Jin-314/IoT-IdeaKit/board/main/pic/v.1/3D_1.png

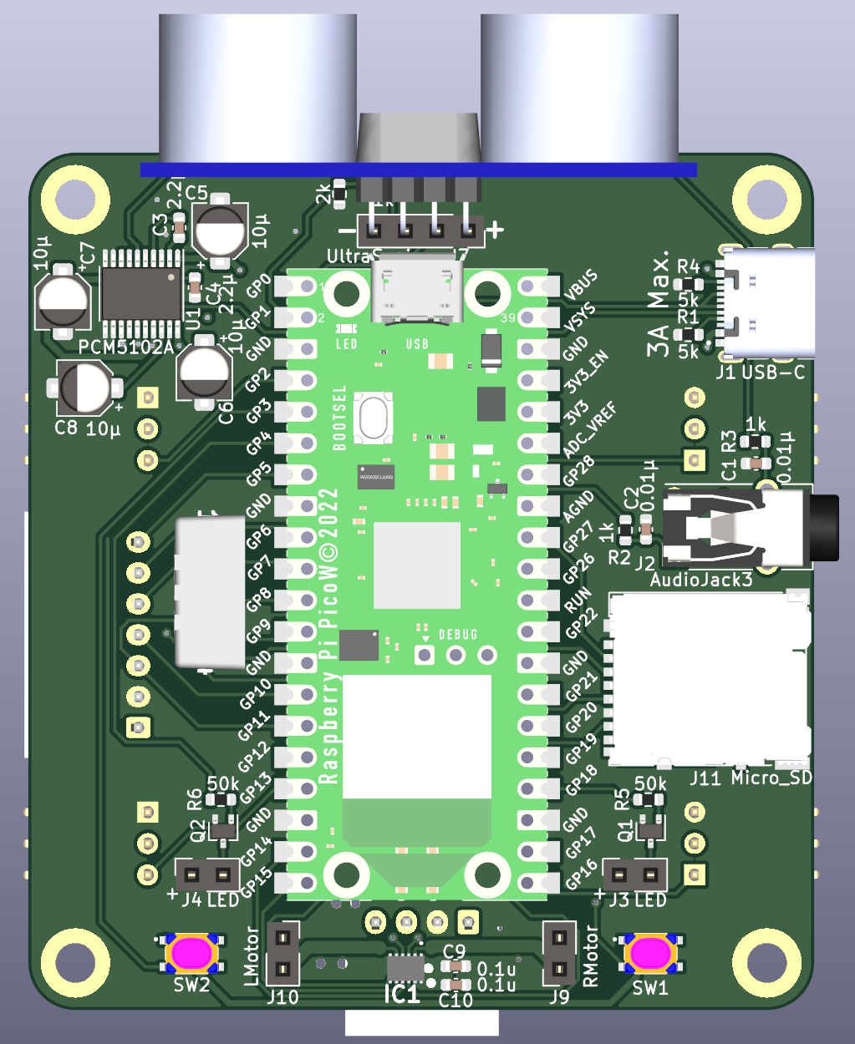
board/main/pic/v.1/3D_1.png
