Jin-314/IoT-IdeaKit/board/main/pic/v.1/PCB_1.png

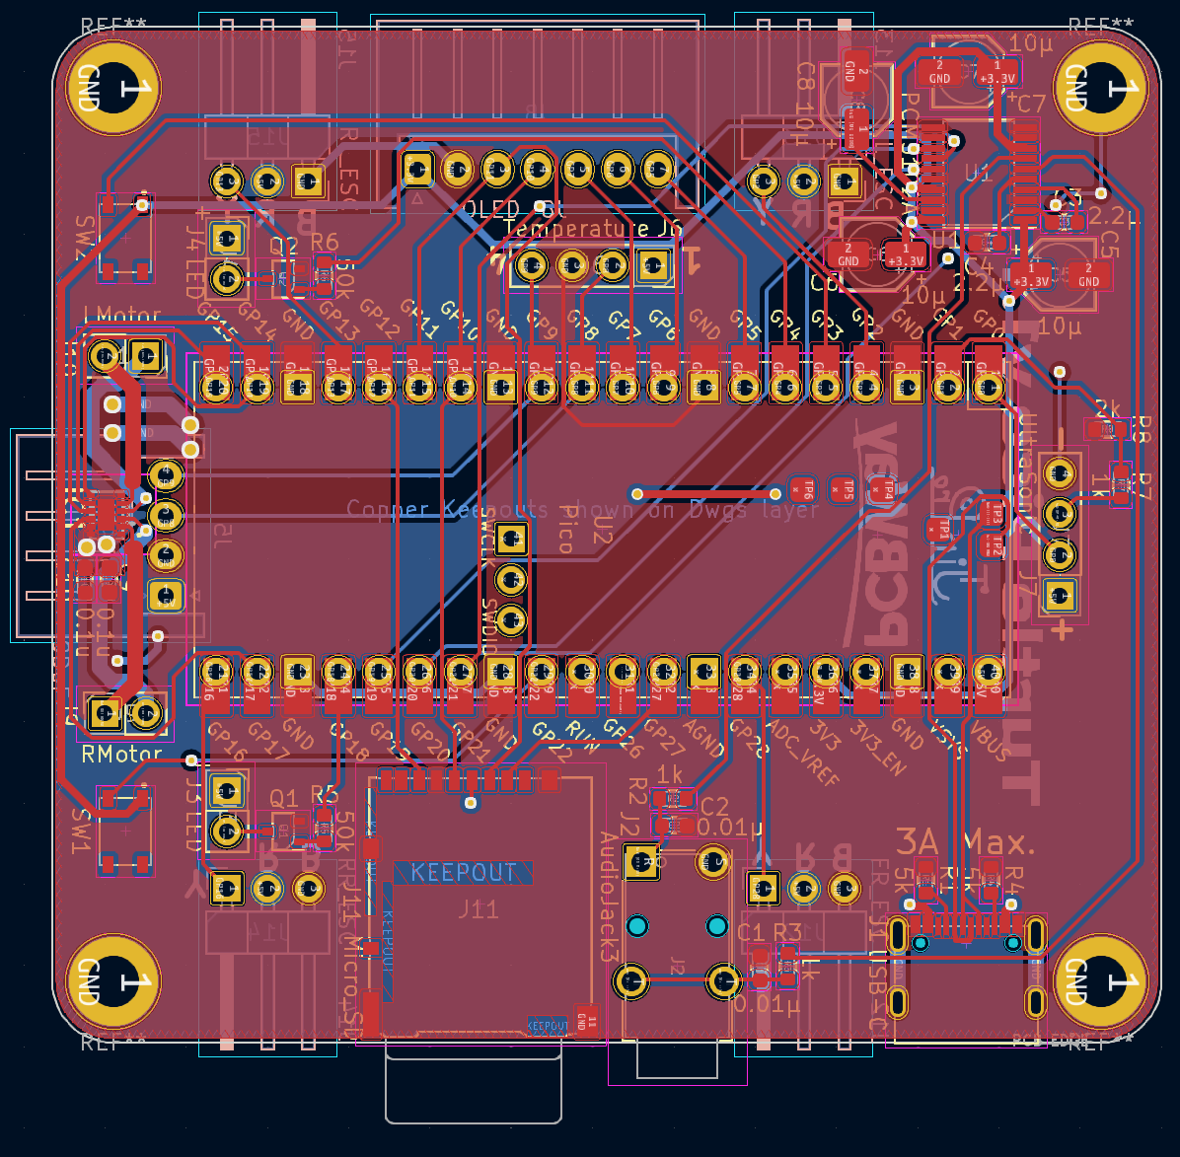
board/main/pic/v.1/PCB_1.png
