Jin-314/IoT-IdeaKit/board/trial/pic/3D_1.png

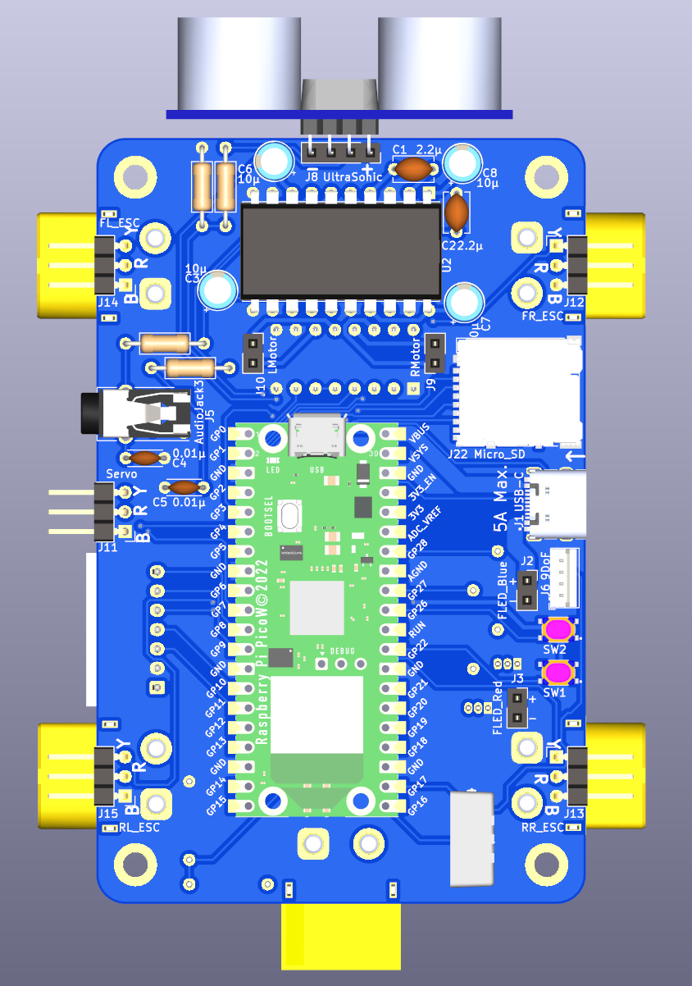
board/trial/pic/3D_1.png
