Jin-314/IoT-IdeaKit/board/trial/pic/3D_2.png

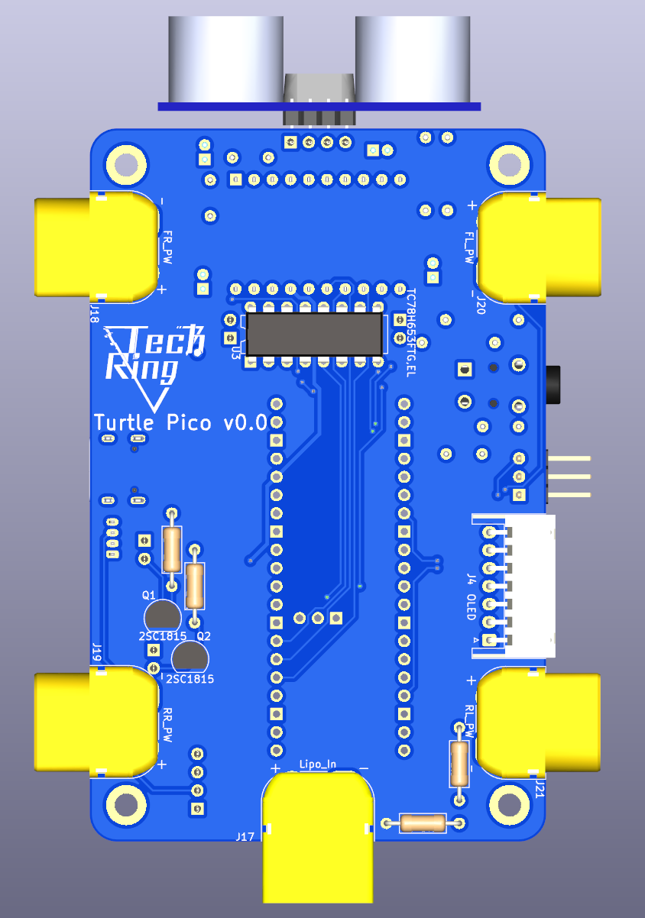
board/trial/pic/3D_2.png
