Jin-314/IoT-IdeaKit/board/trial/pic/PCB_1.png

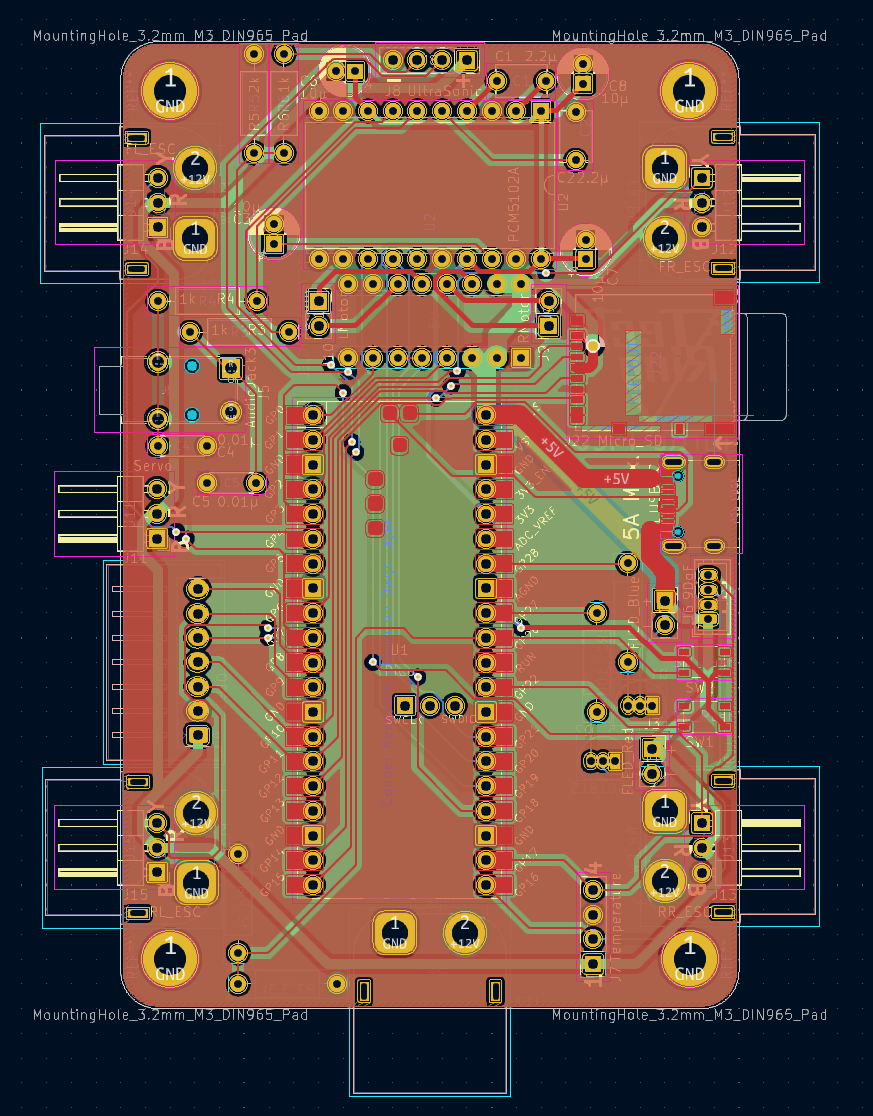
board/trial/pic/PCB_1.png
