Jin-314/IoT-IdeaKit/board/trial/pic/PCB_2.png

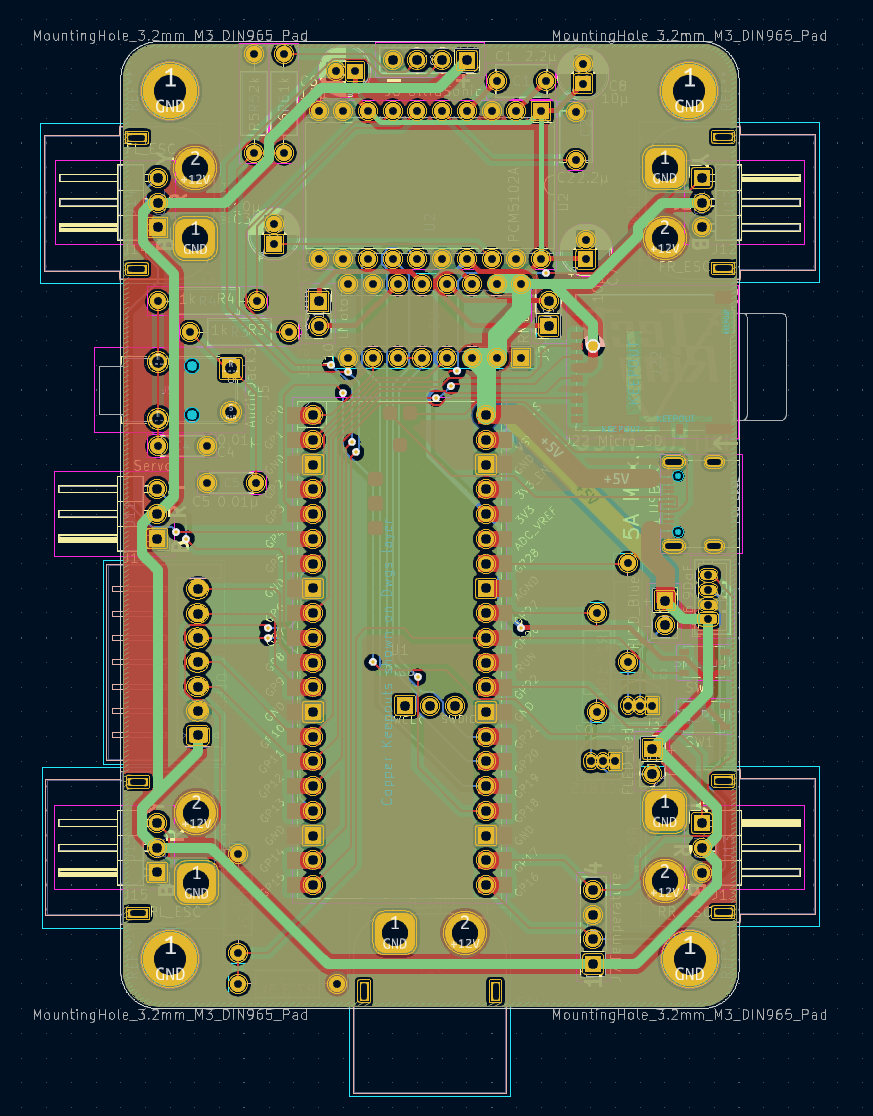
board/trial/pic/PCB_2.png
