Jin-314/IoT-IdeaKit/board/trial/pic/PCB_3.png

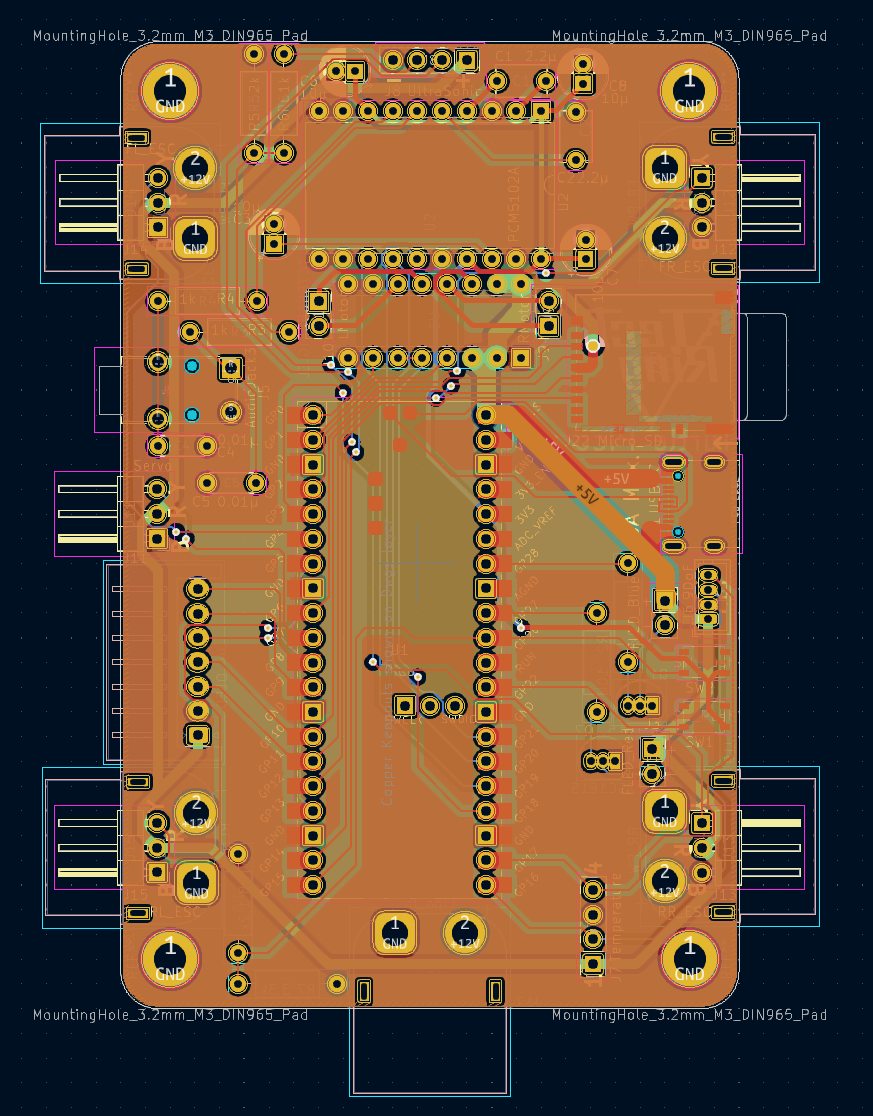
board/trial/pic/PCB_3.png
