Jin-314/IoT-IdeaKit/example/Ironman/main.py

import time
from machine import Pin
from machine import PWM
import neopixel
from lib.TurtlePico import TurtlePico

pixelNum = 15

#ピンを設定
trig = Pin(TurtlePico.TRIG_TX, Pin.OUT)
echo = Pin(TurtlePico.ECHO_RX, Pin.IN)

np3 = neopixel.NeoPixel(Pin(TurtlePico.ESC_SERVO_RR), pixelNum)
np2 = neopixel.NeoPixel(Pin(TurtlePico.ESC_SERVO_FR), pixelNum)
np1 = neopixel.NeoPixel(Pin(TurtlePico.ESC_SERVO_FL), pixelNum)

red = Pin(TurtlePico.LED_L, Pin.OUT)
blue = Pin(TurtlePico.LED_R, Pin.OUT)

sig_red = PWM(red)
sig_blue = PWM(blue)

sig_red.freq(1000)
sig_blue.freq(1000)

status = False

while True:
    #トリガから超音波出力
    trig.low()
    time.sleep_us(2)
    trig.high()
    time.sleep_us(10)
    trig.low()
    signaloff, signalon = 0, 0
    tmout_cnt = 0
    #echoに返ってくるまでの時間を計測
    while echo.value() == 0:
        signaloff = time.ticks_us()
        tmout_cnt += 1
        if tmout_cnt > 2000 :
            break
    while echo.value() == 1:
        signalon = time.ticks_us()
    timepassed = signalon - signaloff
    distance = (timepassed * 0.0343) / 2
    #logging
    print("dinstance: ",distance,"cm")

    if distance < 15 and status == False:
        status = True
        for i in range(pixelNum):
            sig_red.duty_u16(int(32768/pixelNum*i))
            sig_blue.duty_u16(int(32768/pixelNum*i))
            np1[i] = (0, 0, 128)
            np2[i] = (0, 0, 128)
            np3[i] = (0, 16, 32)
            np1.write()
            np2.write()
            np3.write()
            time.sleep_ms(25)
    elif distance > 15 and status == True:
        status = False
        sig_red.duty_u16(0)
        sig_blue.duty_u16(0)
        for i in range(15):
            np1[i] = (0, 0, 0)
            np2[i] = (0, 0, 0)
            np3[i] = (0, 0, 0)
            np1.write()
            np2.write()
            np3.write()
            time.sleep_ms(25)

    time.sleep(0.5)
